bobm123/COGDisplayBreakout/docs/erc12864-11_Outline.png

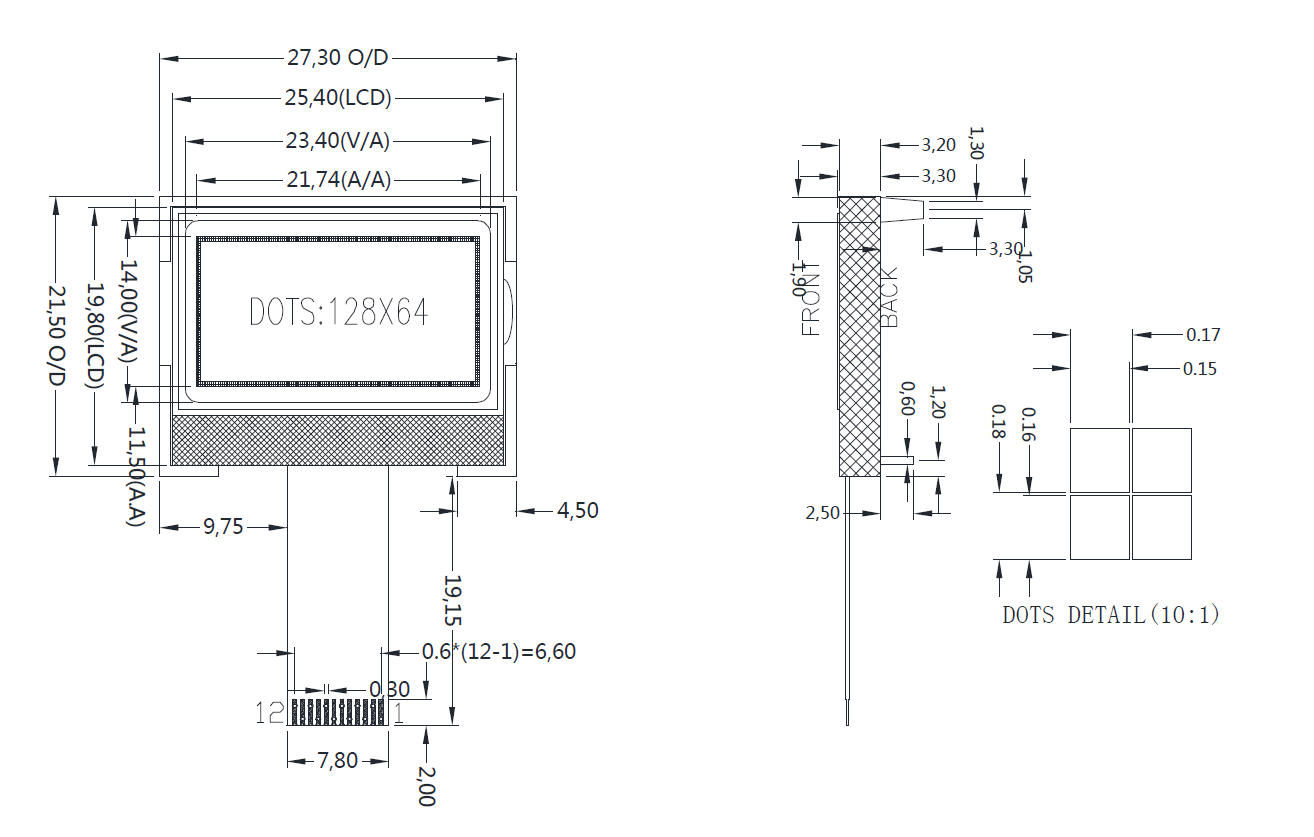
docs/erc12864-11_Outline.png
